SFaull/TankTempMonitorPro/firmware/src/image.h

 #include <stdint.h>
 
const uint8_t tank_outline [] = {
0x00, 0x00, 0x00, 0x00, 0x00, 0x00, 0x00, 0x00, 0x00, 0x00, 0x00, 0x00, 0x00, 0x00, 0x00, 0x00, 
0x00, 0x00, 0x00, 0x00, 0x00, 0x00, 0x07, 0xff, 0xf0, 0x00, 0x00, 0x00, 0x00, 0x00, 0x00, 0x00, 
0x00, 0x00, 0x00, 0x00, 0x00, 0x03, 0xff, 0xff, 0xff, 0xe0, 0x00, 0x00, 0x00, 0x00, 0x00, 0x00, 
0x00, 0x00, 0x00, 0x00, 0x00, 0x3f, 0xff, 0xff, 0xff, 0xfe, 0x00, 0x00, 0x00, 0x00, 0x00, 0x00, 
0x00, 0x00, 0x00, 0x00, 0x01, 0xff, 0xf8, 0x00, 0x0f, 0xff, 0xc0, 0x00, 0x00, 0x00, 0x00, 0x00, 
0x00, 0x00, 0x00, 0x00, 0x0f, 0xfe, 0x00, 0x00, 0x00, 0x3f, 0xf8, 0x00, 0x00, 0x00, 0x00, 0x00, 
0x00, 0x00, 0x00, 0x00, 0x3f, 0xc0, 0x00, 0x00, 0x00, 0x01, 0xff, 0x00, 0x00, 0x00, 0x00, 0x00, 
0x00, 0x00, 0x00, 0x01, 0xfe, 0x00, 0x00, 0x00, 0x00, 0x00, 0x3f, 0xc0, 0x00, 0x00, 0x00, 0x00, 
0x00, 0x00, 0x00, 0x07, 0xf8, 0x00, 0x00, 0x00, 0x00, 0x00, 0x07, 0xf0, 0x00, 0x00, 0x00, 0x00, 
0x00, 0x00, 0x00, 0x1f, 0xc0, 0x00, 0x00, 0x00, 0x00, 0x00, 0x01, 0xfc, 0x00, 0x00, 0x00, 0x00, 
0x00, 0x00, 0x00, 0x3f, 0x00, 0x00, 0x00, 0x00, 0x00, 0x00, 0x00, 0x7e, 0x00, 0x00, 0x00, 0x00, 
0x00, 0x00, 0x00, 0xfc, 0x00, 0x00, 0x00, 0x00, 0x00, 0x00, 0x00, 0x1f, 0x80, 0x00, 0x00, 0x00, 
0x00, 0x00, 0x01, 0xf0, 0x00, 0x00, 0x00, 0x00, 0x00, 0x00, 0x00, 0x07, 0xe0, 0x00, 0x00, 0x00, 
0x00, 0x00, 0x07, 0xe0, 0x00, 0x00, 0x00, 0x00, 0x00, 0x00, 0x00, 0x01, 0xf0, 0x00, 0x00, 0x00, 
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
0x07, 0xff, 0x0f, 0xa0, 0x27, 0xf8, 0xff, 0xe0, 0x00, 0x00, 
0x03, 0xff, 0x1f, 0xe1, 0x06, 0x9c, 0xff, 0xc0, 0x00, 0x00, 
0x03, 0xff, 0xbf, 0xe8, 0x00, 0x1d, 0xff, 0xc0, 0x00, 0x00, 
0x03, 0xff, 0x3e, 0x34, 0x22, 0x80, 0xff, 0xc0, 0x00, 0x00, 
0x03, 0xff, 0xac, 0x04, 0x2b, 0xc9, 0xff, 0xc0, 0x00, 0x00, 
0x03, 0xff, 0x00, 0xd0, 0x07, 0xfc, 0xff, 0xc0, 0x00, 0x00, 
0x03, 0xff, 0x10, 0xf1, 0x91, 0xfd, 0xff, 0xc0, 0x00, 0x00, 
0x03, 0xff, 0x0f, 0xe0, 0x3a, 0xf0, 0xff, 0xe0, 0x00, 0x00, 
0x03, 0xff, 0xcf, 0xd5, 0x77, 0xf3, 0xff, 0xc0, 0x00, 0x00, 
0x03, 0xff, 0xdf, 0xfa, 0x7b, 0xfb, 0xff, 0xe0, 0x00, 0x00, 
0x01, 0xff, 0x87, 0xb6, 0x3d, 0xa1, 0xff, 0xc0, 0x00, 0x00, 
0x01, 0xff, 0xeb, 0x7e, 0x1f, 0xd7, 0xff, 0x80, 0x00, 0x00, 
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
};
