SFaull/TankTempMonitorPro/firmware/src/version.h

#define VERSION_MAJOR 2
#define VERSION_MINOR 1
#define VERSION_PATCH 0

#define STRINGIFY(x) #x
#define STR(x) STRINGIFY(x)

#define VERSION_STRING "v" STR(VERSION_MAJOR) "." STR(VERSION_MINOR) "." STR(VERSION_PATCH)
