SFaull/TankTempMonitorPro/firmware/src/ds18b20.h

#include <OneWire.h>
#include <DallasTemperature.h>
#include "config.h"

#define RESOLUTION 12

// TODO: implement some form of rolling average
typedef struct 
{
  DeviceAddress address;
  float temperature = -99.0;
  float temperatureAve = -99.0;
  float offset = 0.0;
  uint16_t sampleCount = 0;
  bool valid = false;
} sensor_t;

extern sensor_t mySensor[SENSOR_COUNT];

void ds18b20_init(void);
void ds18b20_request(void);
void ds18b20_getTemp(void);
int ds18b20_get_device_count(void);
bool ds18b20_get_error(void);
